flafforgue/16MidiButtons/Photos/IMG_20230427_181406.jpg

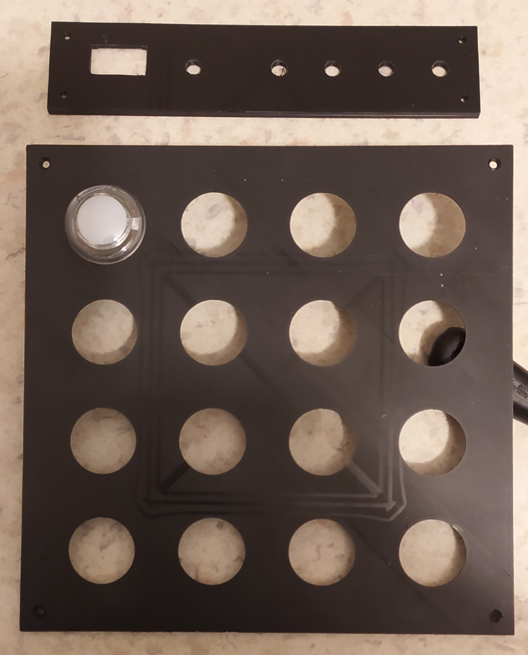
Photos/IMG_20230427_181406.jpg
