flafforgue/16MidiButtons/Photos/IMG_20230501_203154.jpg

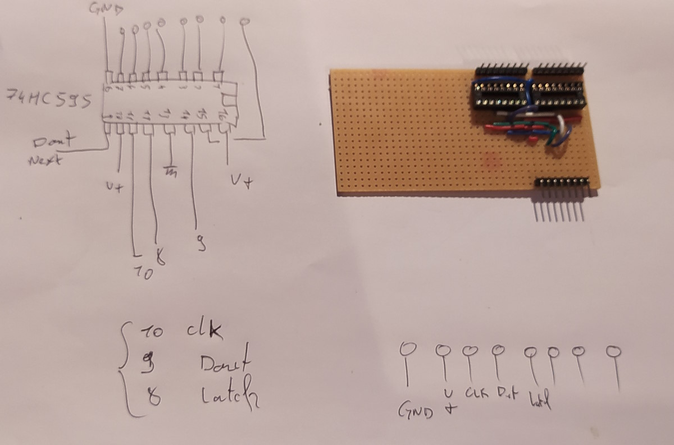
Photos/IMG_20230501_203154.jpg
